IdleHandsProject/pixopixel/FIRMWARE/PIXO_WIP/image.h

int twitter[256][3] = {{40, 170, 225}, {40, 170, 225}, {40, 170, 225}, {40, 170, 225}, {40, 170, 225}, {40, 170, 225}, {40, 170, 225}, {40, 170, 225}, {40, 170, 225}, {40, 170, 225}, {40, 170, 225}, {40, 170, 225}, {40, 170, 225}, {40, 170, 225}, {40, 170, 225}, {40, 170, 225}, {40, 170, 225}, {40, 170, 225}, {40, 170, 225}, {40, 170, 225}, {40, 170, 225}, {40, 170, 225}, {40, 170, 225}, {40, 170, 225}, {40, 170, 225}, {42, 171, 225}, {43, 171, 225}, {40, 170, 225}, {40, 170, 225}, {40, 170, 225}, {40, 170, 225}, {40, 170, 225}, {40, 170, 225}, {40, 170, 225}, {40, 170, 225}, {42, 171, 225}, {41, 170, 225}, {40, 170, 225}, {40, 170, 225}, {41, 170, 225}, {41, 170, 225}, {29, 166, 223}, {28, 165, 223}, {40, 170, 225}, {39, 169, 225}, {39, 170, 225}, {40, 170, 225}, {40, 170, 225}, {40, 170, 225}, {40, 170, 225}, {40, 170, 225}, {30, 166, 224}, {37, 169, 225}, {44, 171, 225}, {41, 170, 225}, {38, 169, 225}, {36, 168, 224}, {96, 192, 233}, {101, 194, 234}, {39, 169, 225}, {43, 171, 225}, {43, 171, 225}, {39, 170, 225}, {40, 170, 225}, {40, 170, 225}, {39, 170, 225}, {42, 171, 225}, {152, 214, 241}, {56, 176, 227}, {24, 164, 223}, {42, 171, 225}, {35, 168, 224}, {169, 221, 243}, {255, 255, 255}, {255, 255, 255}, {212, 238, 249}, {171, 221, 243}, {50, 174, 226}, {38, 169, 225}, {41, 170, 225}, {40, 170, 225}, {40, 170, 225}, {35, 168, 224}, {230, 245, 252}, {224, 242, 251}, {99, 193, 233}, {34, 167, 224}, {58, 177, 227}, {255, 255, 255}, {253, 254, 255}, {250, 253, 254}, {255, 255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
 {234, 142, 20}, {247, 117, 1}, {255, 107, 0}, {255, 70, 0}, {255, 40, 0}, {255, 11, 2}, {255, 6, 15}, {255, 15, 40}, {247, 21, 57}, {236, 30, 78}, {212, 37, 97}, {187, 42, 110}, {181, 52, 136}, {180, 59, 154}, {245, 212, 4}, {255, 225, 0}, {247, 183, 3}, {236, 132, 18}, {252, 115, 4}, {249, 84, 1}, {244, 54, 1}, {246, 24, 0}, {246, 0, 1}, {242, 5, 19}, {234, 15, 41}, {229, 25, 68}, {202, 32, 78}, {203, 35, 94}, {219, 49, 129}, {183, 50, 129}, {245, 218, 18}, {247, 214, 2}, {255, 224, 0}, {247, 181, 1}, {244, 159, 2}, {247, 135, 5}, {244, 107, 2}, {246, 79, 2}, {244, 49, 2}, {246, 16, 0}, {246, 2, 5}, {235, 9, 24}, {227, 19, 52}, {243, 32, 83}, {206, 36, 95}, {196, 39, 107}, {0, 0, 0}, {245, 217, 18}, {250, 217, 4}, {249, 201, 1}, {255, 188, 2}, {255, 155, 1}, {255, 124, 1}, {255, 94, 1}, {255, 64, 1}, {255, 33, 1}, {255, 8, 3}, {255, 7, 19}, {238, 14, 38}, {228, 21, 57}, {205, 29, 58}, {0, 0, 0}};
int upvote[256][3] = {{0, 0, 0}, {0, 0, 0}, {0, 0, 0}, {0, 0, 0}, {0, 0, 0}, {0, 0, 0}, {0, 0, 0}, {0, 0, 0}, {0, 0, 0}, {0, 0, 0}, {0, 0, 0}, {0, 0, 0}, {0, 0, 0}, {0, 0, 0}, {0, 0, 0}, {0, 0, 0}, {0, 0, 0}, {0, 0, 0}, {0, 0, 0}, {0, 0, 0}, {0, 0, 0}, {0, 0, 0}, {0, 0, 0}, {255, 68, 0}, {255, 68, 0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
int sh[256][3] = {{0, 0, 0}, {0, 0, 0}, {0, 0, 0}, {0, 0, 0}, {0, 0, 0}, {0, 0, 0}, {0, 0, 0}, {0, 0, 0}, {0, 0, 0}, {0, 0, 0}, {0, 0, 0}, {0, 0, 0}, {0, 0, 0}, {0, 0, 0}, {0, 0, 0}, {0, 0, 0}, {0, 0, 0}, {0, 0, 0}, {1, 1, 1}, {2, 2, 2}, {3, 3, 3}, {3, 3, 3}, {2, 2, 2}, {0, 0, 0}, {0, 0, 0}, {0, 0, 0}, {0, 0, 0}, {0, 0, 0}, {0, 0, 0}, {0, 0, 0}, {0, 0, 0}, {0, 0, 0}, {3, 3, 3}, {3, 3, 3}, {0, 0, 0}, {0, 0, 0}, {0, 0, 0}, {0, 0, 0}, {0, 0, 0}, {0, 0, 0}, {0, 0, 0}, {0, 0, 0}, {0, 0, 0}, {0, 0, 0}, {0, 0, 0}, {0, 0, 0}, {0, 0, 0}, {0, 0, 0}, {0, 0, 0}, {0, 0, 0}, {22, 22, 22}, {58, 58, 58}, {78, 78, 78}, {86, 86, 86}, {69, 69, 69}, {5, 5, 5}, {1, 1, 1}, {3, 3, 3}, {0, 0, 0}, {2, 2, 2}, {0, 0, 0}, {0, 0, 0}, {0, 0, 0}, {0, 0, 0}, {86, 86, 86}, {154, 154, 154}, {114, 114, 114}, {73, 73, 73}, {49, 49, 49}, {40, 40, 40}, {39, 39, 39}, {6, 6, 6}, {0, 0, 0}, {0, 0, 0}, {0, 0, 0}, {0, 0, 0}, {0, 0, 0}, {0, 0, 0}, {0, 0, 0}, {0, 0, 0}, {93, 93, 93}, {163, 163, 163}, {118, 118, 118}, {65, 65, 65}, {17, 17, 17}, {0, 0, 0}, {0, 0, 0}, {1, 1, 1}, {14, 14, 14}, {52, 52, 52}, {0, 0, 0}, {35, 35, 35}, {0, 0, 0}, {2, 2, 2}, {3, 3, 3}, {2, 2, 2}, {0, 0, 0}, {0, 0, 0}, {30, 30, 30}, {74, 74, 74}, {114, 114, 114}, {122, 122, 122}, {54, 54, 54}, {0, 0, 0}, {21, 21, 21}, {211, 211, 211}, {4, 4, 4}, {174, 174, 174}, {48, 48, 48}, {0, 0, 0}, {0, 0, 0}, {0, 0, 0}, {3, 3, 3}, {2, 2, 2}, {0, 0, 0}, {0, 0, 0}, {0, 0, 0}, {32, 32, 32}, {131, 131, 131}, {108, 108, 108}, {0, 0, 0}, {183, 183, 183}, {38, 38, 38}, {136, 136, 136}, {130, 130, 130}, {41, 41, 41}, {75, 75, 75}, {78, 78, 78}, {0, 0, 0}, {0, 0, 0}, {2, 2, 2}, {0, 0, 0}, {0, 0, 0}, {20, 20, 20}, {51, 51, 51}, {199, 199, 199}, {152, 152, 152}, {199, 199, 199}, {116, 116, 116}, {110, 110, 110}, {193, 193, 193}, {51, 51, 51}, {46, 46, 46}, {25, 25, 25}, {0, 0, 0}, {1, 1, 1}, {0, 0, 0}, {61, 61, 61}, {154, 154, 154}, {123, 123, 123}, {76, 76, 76}, {53, 53, 53}, {173, 173, 173}, {155, 155, 155}, {123, 123, 123}, {0, 0, 0}, {181, 181, 181}, {4, 4, 4}, {0, 0, 0}, {0, 0, 0}, {2, 2, 2}, {0, 0, 0}, {49, 49, 49}, {209, 209, 209}, {32, 32, 32}, {0, 0, 0}, {0, 0, 0}, {117, 117, 117}, {126, 126, 126}, {53, 53, 53}, {135, 135, 135}, {1, 1, 1}, {134, 134, 134}, {63, 63, 63}, {2, 2, 2}, {3, 3, 3}, {1, 1, 1}, {1, 1, 1}, {24, 24, 24}, {124, 124, 124}, {87, 87, 87}, {75, 75, 75}, {126, 126, 126}, {143, 143, 143}, {11, 11, 11}, {0, 0, 0}, {0, 0, 0}, {0, 0, 0}, {53, 53, 53}, {126, 126, 126}, {0, 0, 0}, {3, 3, 3}, {0, 0, 0}, {0, 0, 0}, {0, 0, 0}, {0, 0, 0}, {25, 25, 25}, {35, 35, 35}, {24, 24, 24}, {0, 0, 0}, {0, 0, 0}, {2, 2, 2}, {3, 3, 3}, {0, 0, 0}, {0, 0, 0}, {35, 35, 35}, {0, 0, 0}, {0, 0, 0}, {0, 0, 0}, {0, 0, 0}, {1, 1, 1}, {2, 2, 2}, {0, 0, 0}, {0, 0, 0}, {0, 0, 0}, {3, 3, 3}, {1, 1, 1}, {0, 0, 0}, {0, 0, 0}, {0, 0, 0}, {0, 0, 0}, {0, 0, 0}, {0, 0, 0}, {0, 0, 0}, {0, 0, 0}, {0, 0, 0}, {0, 0, 0}, {0, 0, 0}, {1, 1, 1}, {1, 1, 1}, {1, 1, 1}, {0, 0, 0}, {0, 0, 0}, {0, 0, 0}, {0, 0, 0}, {0, 0, 0}, {0, 0, 0}, {1, 1, 1}, {0, 0, 0}, {0, 0, 0}, {0, 0, 0}, {0, 0, 0}, {0, 0, 0}, {0, 0, 0}, {0, 0, 0}, {0, 0, 0}, {0, 0, 0}, {0, 0, 0}, {0, 0, 0}, {0, 0, 0}, {0, 0, 0}, {0, 0, 0}, {0, 0, 0}, {0, 0, 0}, {0, 0, 0}, {0, 0, 0}};
int glogo[256][3] = {{255, 255, 255}, {255, 255, 255}, {255, 255, 255}, {255, 255, 255}, {255, 255, 255}, {255, 255, 255}, {255, 255, 255}, {0, 0, 0}, {0, 0, 0}, {11, 11, 11}, {255, 255, 255}, {255, 255, 255}, {255, 255, 255}, {255, 255, 255}, {255, 255, 255}, {255, 255, 255}, {255, 255, 255}, {255,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
//int mario[256][3] = {{0, 0, 0}, {0, 0, 0}, {0, 0, 0}, {0, 0, 0}, {0, 0, 0}, {216, 0, 0}, {216, 0, 0}, {216, 0, 0}, {216, 0, 0}, {216, 0, 0}, {0, 0, 0}, {0, 0, 0}, {0, 0, 0}, {0, 0, 0}, {0, 0, 0}, {0, 0, 0}, {0, 0, 0}, {0, 0, 0}, {0, 0, 0}, {0, 0, 0}, {216, 0, 0}, {216, 0, 0}, {216, 0, 0}, {216, 0,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
